domchom/domiframe/web/sample.jpg

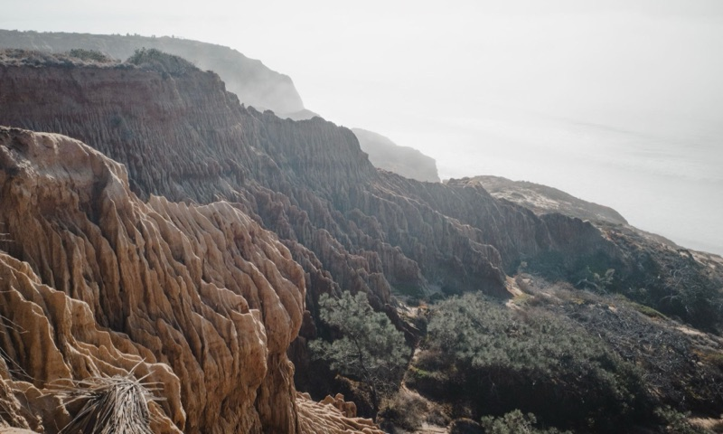
web/sample.jpg
