domchom/domiframe/enclosure/door-preview.png

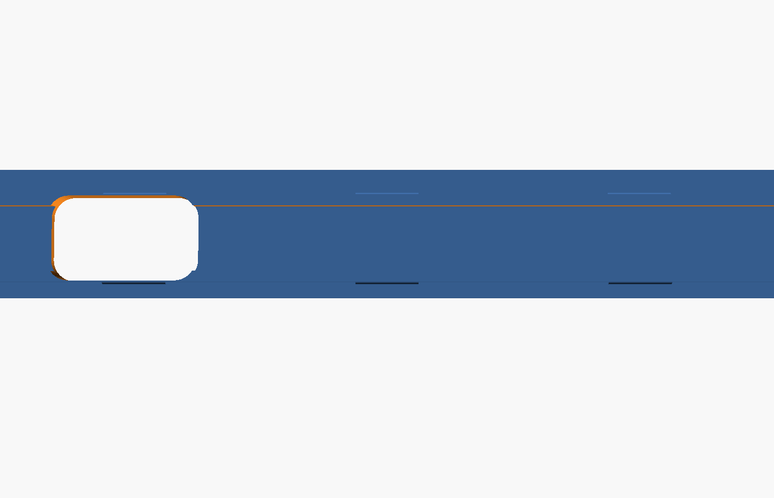
enclosure/door-preview.png
