domchom/domiframe/web/og-invite.png

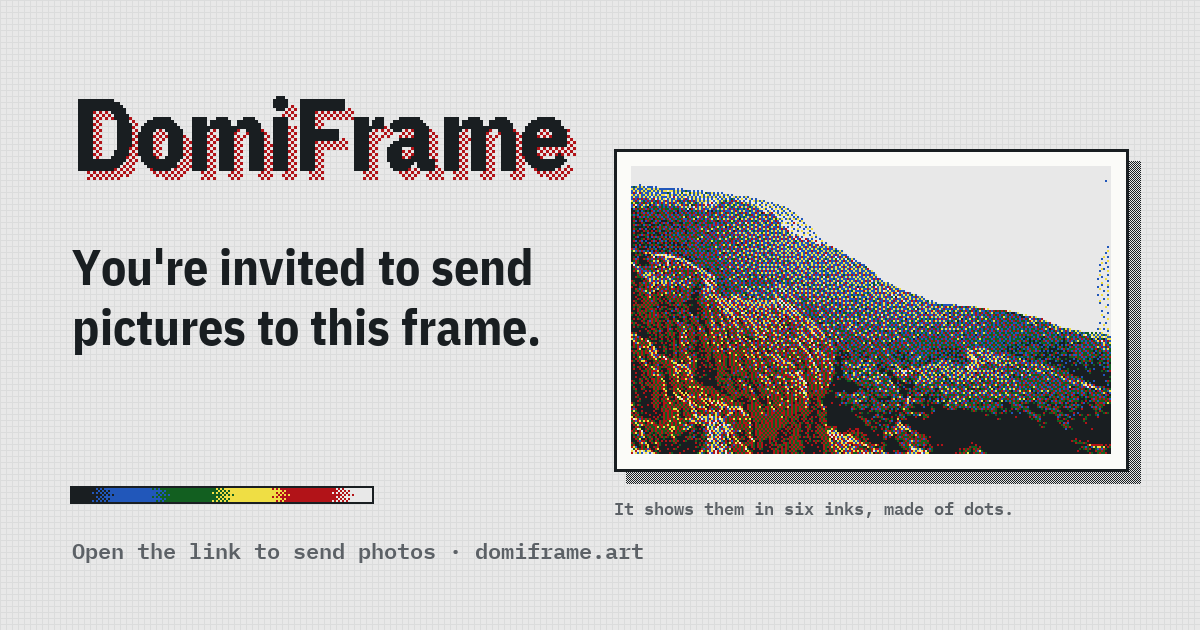
web/og-invite.png
