domchom/domiframe/firmware/include/plex_fonts.h

// Made by tools/make_fonts.py from IBM Plex (tools/fonts, SIL Open Font License): don't edit.
// The frame's fonts at its own size: the 13.3" ones are twice the 7.3"'s, for its pixels.
#pragma once

#if defined(DOMIFRAME_PANEL_13IN3)
const uint8_t PlexTitle_Bitmaps[] PROGMEM = {
  0x7F, 0xE7, 0xFE, 0x7F, 0xE7, 0xFE, 0x7F, 0xE7, 0xFE, 0x7F, 0xE7, 0xFE, 0x7F, 0xE7, 0xFE, 0x7F, 0xE7, 0xFE, 0x7F, 0xE7, 0xFE, 0x7F, 0xE7, 0xFE,
  0x7F, 0xC3, 0xFC, 0x3F, 0xC3, 0xFC, 0x3F, 0xC3, 0xFC, 0x3F, 0x81, 0xF8, 0x1F, 0x81, 0xF8, 0x1F, 0x81, 0xF8, 0x1F, 0x81, 0xF0, 0x0F, 0x00, 0xF0,
  0x00, 0x00, 0x00, 0x00, 0x00, 0x00, 0x1F, 0x87, 0xFC, 0x7F, 0xEF, 0xFE, 0xFF, 0xFF, 0xFF, 0xFF, 0xFF, 0xFF, 0xFF, 0xE7, 0xFE, 0x7F, 0xC1, 0xF8,
  0xFF, 0x83, 0xFF, 0xFF, 0x07, 0xFF, 0xFE, 0x0F, 0xFF, 0xFC, 0x1F, 0xFF, 0xF8, 0x3F, 0xFF, 0xF0, 0x7F, 0xFF, 0xE0, 0xFF, 0xFF, 0xC1, 0xFF, 0xFF,
  0x83, 0xFF, 0xFF, 0x07, 0xFF, 0xFE, 0x0F, 0xFF, 0xFC, 0x1F, 0xFF, 0xF8, 0x3F, 0xFF, 0xF0, 0x7F, 0xFF, 0xE0, 0xFF, 0xFF, 0xC1, 0xFF, 0xFF, 0x83,
  0xFF, 0xFF, 0x07, 0xFF, 0xFE, 0x0F, 0xFF, 0xFC, 0x1F, 0xFF, 0xF8, 0x3F, 0xFF, 0xF0, 0x7F, 0xC0, 0x00, 0x0F, 0xC0, 0x0F, 0xC0, 0x00, 0x3E, 0x00,
  0x3E, 0x00, 0x00, 0xF8, 0x00, 0xF8, 0x00, 0x07, 0xE0, 0x07, 0xE0, 0x00, 0x1F, 0x80, 0x1F, 0x80, 0x00, 0x7E, 0x00, 0x7E, 0x00, 0x01, 0xF8, 0x01,
  0xF8, 0x00, 0x07, 0xC0, 0x07, 0xC0, 0x00, 0x1F, 0x00, 0x1F, 0x00, 0x00, 0xFC, 0x00, 0xFC, 0x00, 0x03, 0xF0, 0x03, 0xF0, 0x07, 0xFF, 0xFF, 0xFF,
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
  {319, 8, 11, 10, 1, -11},  // 0x44 'D'
  {330, 7, 11, 10, 1, -11},  // 0x45 'E'
  {340, 8, 11, 10, 1, -11},  // 0x46 'F'
  {351, 8, 11, 10, 1, -11},  // 0x47 'G'
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
};
const GFXfont PlexIdS PROGMEM = {(uint8_t*)PlexIdS_Bitmaps, (GFXglyph*)PlexIdS_Glyphs, 0x20, 0x7E, 22};

#endif
