domchom/domiframe/firmware/include/pixel_font.h

// Made by scripts/make-pixel-font.py in the app's repo (domiframe-app): don't edit, run it again.
// Pixel letters for the frame's own screens, the same as the website's and the app's wordmark
// (web/pixelfont.js), and the frame code's characters (distinct from their look-alikes).
#pragma once

static const int PF_CAP = 10, PF_SPACING = 2;
struct PfGlyph { char c; int w; const char* rows[10]; };
static const PfGlyph PF_WORD[] = {
    {'D', 7, {"#####..", "######.", "##..###", "##...##", "##...##", "##...##", "##...##", "##..###", "######.", "#####.."}},
    {'F', 6, {"######", "######", "##....", "##....", "#####.", "#####.", "##....", "##....", "##....", "##...."}},
    {'V', 7, {"##...##", "##...##", "##...##", "##...##", "##...##", "###.###", ".##.##.", ".#####.", "..###..", "...#..."}},
    {'a', 6, {"......", "......", "......", "#####.", "######", "....##", ".#####", "##..##", "######", ".#####"}},
    {'d', 6, {"....##", "....##", "....##", ".#####", "######", "##..##", "##..##", "##..##", "######", ".#####"}},
    {'e', 6, {"......", "......", "......", ".####.", "######", "##..##", "######", "##....", "######", ".#####"}},
    {'f', 5, {"..###", ".####", ".##..", "#####", "#####", ".##..", ".##..", ".##..", ".##..", ".##.."}},
    {'i', 2, {"##", "##", "..", "##", "##", "##", "##", "##", "##", "##"}},
    {'l', 2, {"##", "##", "##", "##", "##", "##", "##", "##", "##", "##"}},
    {'m', 8, {"........", "........", "........", "#######.", "########", "##.##.##", "##.##.##", "##.##.##", "##.##.##", "##.##.##"}},
    {'n', 6, {"......", "......", "......", "#####.", "######", "##..##", "##..##", "##..##", "##..##", "##..##"}},
    {'o', 6, {"......", "......", "......", ".####.", "######", "##..##", "##..##", "##..##", "######", ".####."}},
    {'r', 5, {".....", ".....", ".....", "##.##", "#####", "###..", "##...", "##...", "##...", "##..."}},
    {'t', 5, {".....", ".##..", ".##..", "#####", "#####", ".##..", ".##..", ".##..", ".####", "..###"}},
    {'u', 6, {"......", "......", "......", "##..##", "##..##", "##..##", "##..##", "##..##", "######", ".#####"}},
    {' ', 3, {"...", "...", "...", "...", "...", "...", "...", "...", "...", "..."}},
};

static const int PF_CODE_W = 5, PF_CODE_H = 7;
struct PfCodeGlyph { char c; const char* rows[7]; };
static const PfCodeGlyph PF_CODE[] = {
    {'0', {".###.", "#...#", "#..##", "#.#.#", "##..#", "#...#", ".###."}},
    {'1', {"..#..", ".##..", "#.#..", "..#..", "..#..", "..#..", "#####"}},
    {'2', {".###.", "#...#", "....#", "...#.", "..#..", ".#...", "#####"}},
    {'3', {"####.", "....#", "....#", ".###.", "....#", "....#", "####."}},
    {'4', {"...#.", "..##.", ".#.#.", "#..#.", "#####", "...#.", "...#."}},
    {'5', {"#####", "#....", "####.", "....#", "....#", "#...#", ".###."}},
    {'6', {"..##.", ".#...", "#....", "####.", "#...#", "#...#", ".###."}},
    {'7', {"#####", "....#", "...#.", "..#..", ".#...", ".#...", ".#..."}},
    {'8', {".###.", "#...#", "#...#", ".###.", "#...#", "#...#", ".###."}},
    {'9', {".###.", "#...#", "#...#", ".####", "....#", "...#.", ".##.."}},
    {'A', {".###.", "#...#", "#...#", "#####", "#...#", "#...#", "#...#"}},
    {'B', {"####.", "#...#", "#...#", "####.", "#...#", "#...#", "####."}},
    {'C', {".###.", "#...#", "#....", "#....", "#....", "#...#", ".###."}},
    {'D', {"###..", "#..#.", "#...#", "#...#", "#...#", "#..#.", "###.."}},
    {'E', {"#####", "#....", "#....", "####.", "#....", "#....", "#####"}},
    {'F', {"#####", "#....", "#....", "####.", "#....", "#....", "#...."}},
    {'G', {".###.", "#...#", "#....", "#.###", "#...#", "#...#", ".####"}},
    {'H', {"#...#", "#...#", "#...#", "#####", "#...#", "#...#", "#...#"}},
    {'J', {"..###", "...#.", "...#.", "...#.", "...#.", "#..#.", ".##.."}},
    {'K', {"#...#", "#..#.", "#.#..", "##...", "#.#..", "#..#.", "#...#"}},
    {'M', {"#...#", "##.##", "#.#.#", "#.#.#", "#...#", "#...#", "#...#"}},
    {'N', {"#...#", "#...#", "##..#", "#.#.#", "#..##", "#...#", "#...#"}},
    {'P', {"####.", "#...#", "#...#", "####.", "#....", "#....", "#...."}},
    {'Q', {".###.", "#...#", "#...#", "#...#", "#.#.#", "#..#.", ".##.#"}},
    {'R', {"####.", "#...#", "#...#", "####.", "#.#..", "#..#.", "#...#"}},
    {'S', {".####", "#....", "#....", ".###.", "....#", "....#", "####."}},
    {'T', {"#####", "..#..", "..#..", "..#..", "..#..", "..#..", "..#.."}},
    {'V', {"#...#", "#...#", "#...#", "#...#", "#...#", ".#.#.", "..#.."}},
    {'W', {"#...#", "#...#", "#...#", "#.#.#", "#.#.#", "##.##", "#...#"}},
    {'X', {"#...#", "#...#", ".#.#.", "..#..", ".#.#.", "#...#", "#...#"}},
    {'Y', {"#...#", "#...#", ".#.#.", "..#..", "..#..", "..#..", "..#.."}},
    {'Z', {"#####", "....#", "...#.", "..#..", ".#...", "#....", "#####"}},
};
